andreiva/simple-rssi-antenna-tracker/servo-mount-3d/parts-screenshot.png

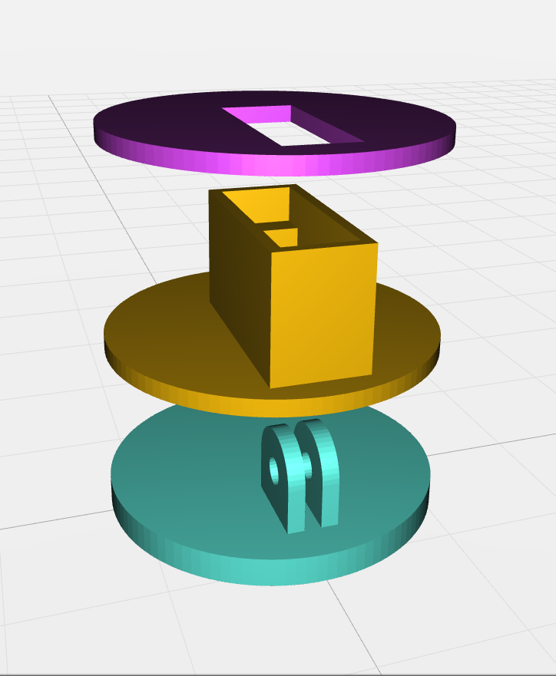
servo-mount-3d/parts-screenshot.png
